MOSH-Insa-Toulouse/2022_Franco_Alonso_Projet_capteur/Images/Rayon_de_courbure_01.jpg

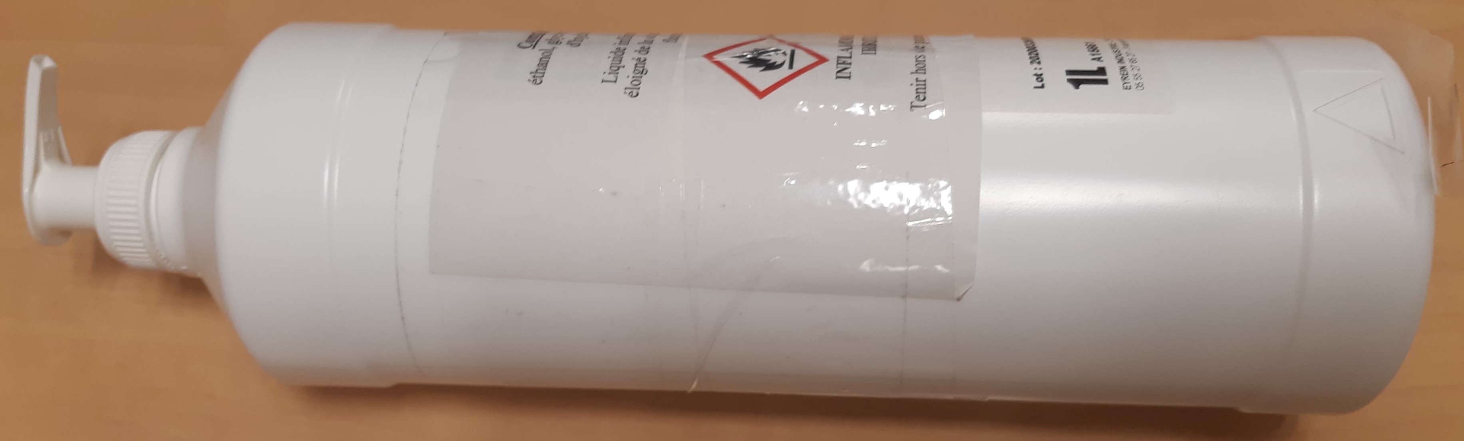
Images/Rayon_de_courbure_01.jpg
