MOSH-Insa-Toulouse/2022_Franco_Alonso_Projet_capteur/Shield PCB/Kicad_capteur_graphite/modele_3D-OLED_0.91/OLED display v2.png

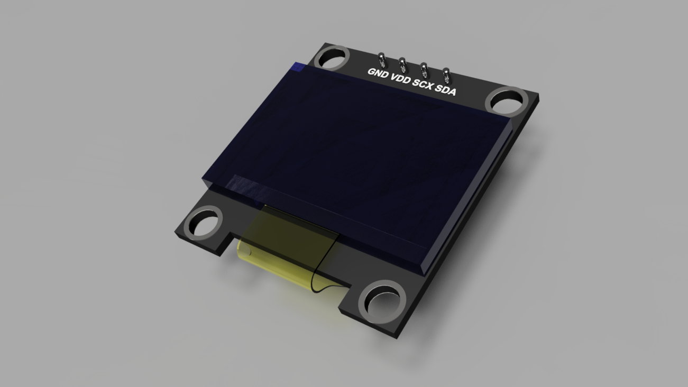
Shield PCB/Kicad_capteur_graphite/modele_3D-OLED_0.91/OLED display v2.png
