MOSH-Insa-Toulouse/2022_Franco_Alonso_Projet_capteur/Shield PCB/Kicad_capteur_graphite/modele_3D-Header-female/1x4.STEP

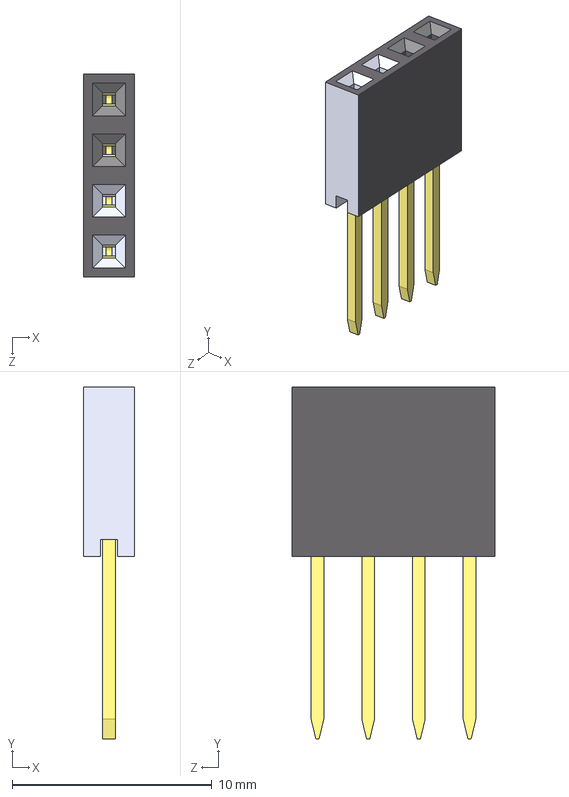
[picture p50: CAD file, 2022-04-12]
Shield PCB/Kicad_capteur_graphite/modele_3D-Header-female/1x4.STEP
2.54 x 17.6 x 10.2 mm
